semsyekeler/Embedded-AI-Vision-Glass/1_Hardware_Design/gozluk-sema-fiziksel.jpg

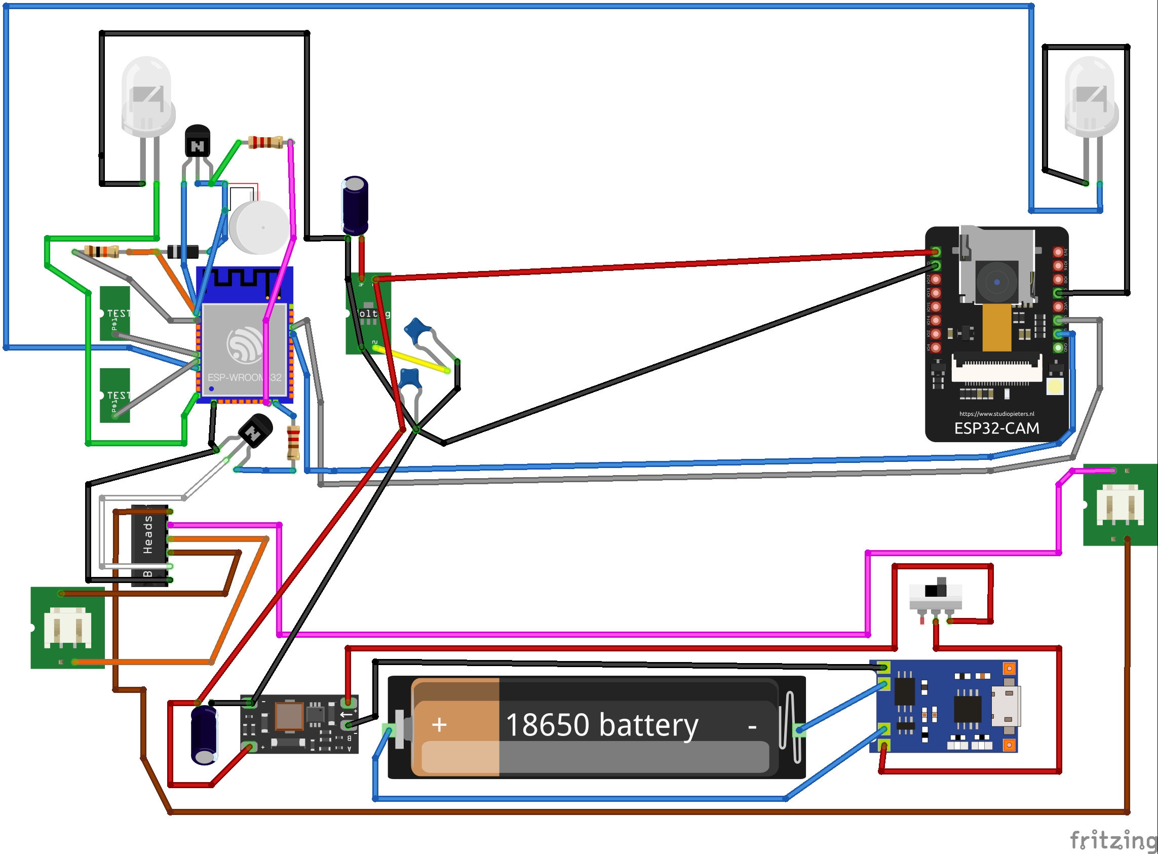
1_Hardware_Design/gozluk-sema-fiziksel.jpg
