semsyekeler/Embedded-AI-Vision-Glass/1_Hardware_Design/gozluk-sema.jpg

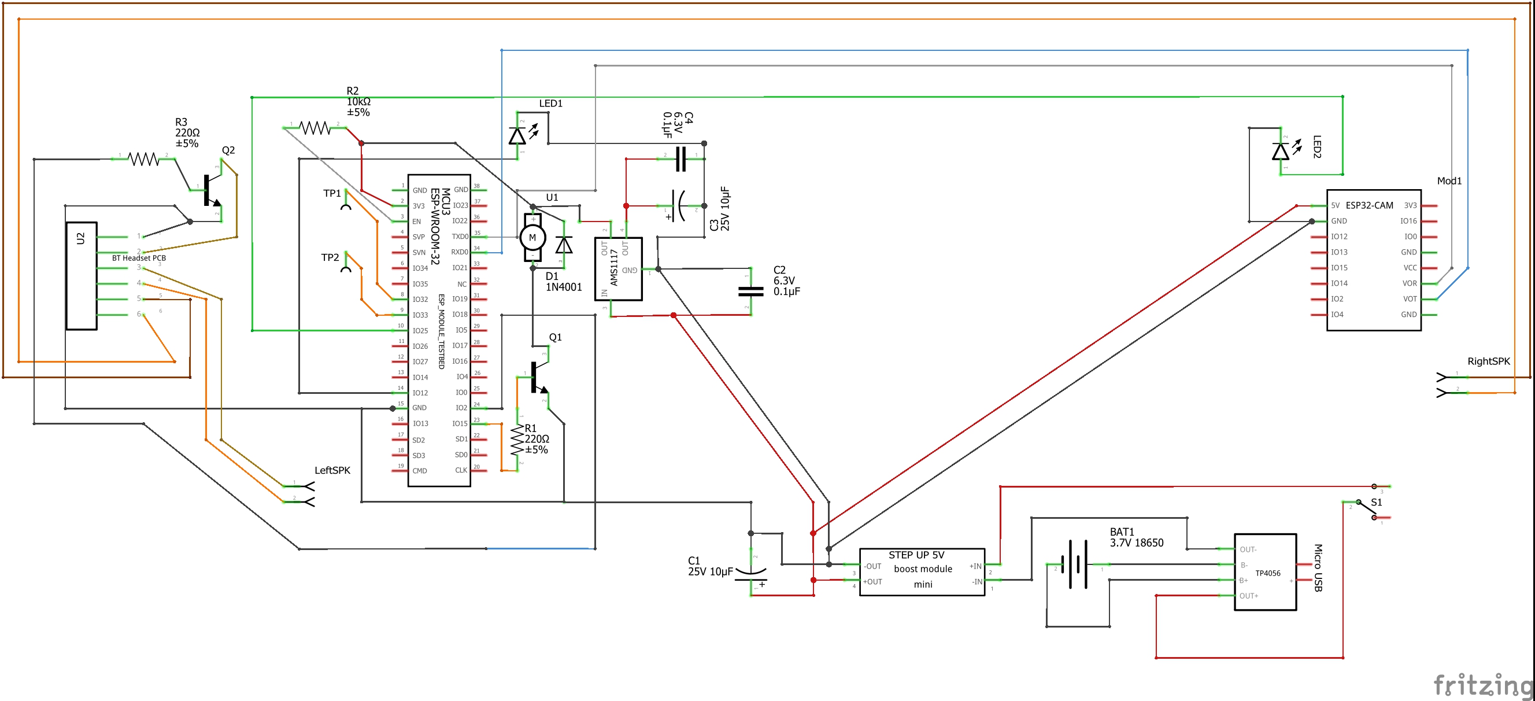
1_Hardware_Design/gozluk-sema.jpg
