semsyekeler/Embedded-AI-Vision-Glass/5_Project_Documentation/Media/2_Competition_and_Awards/award-pose-shoot-upside.jpg

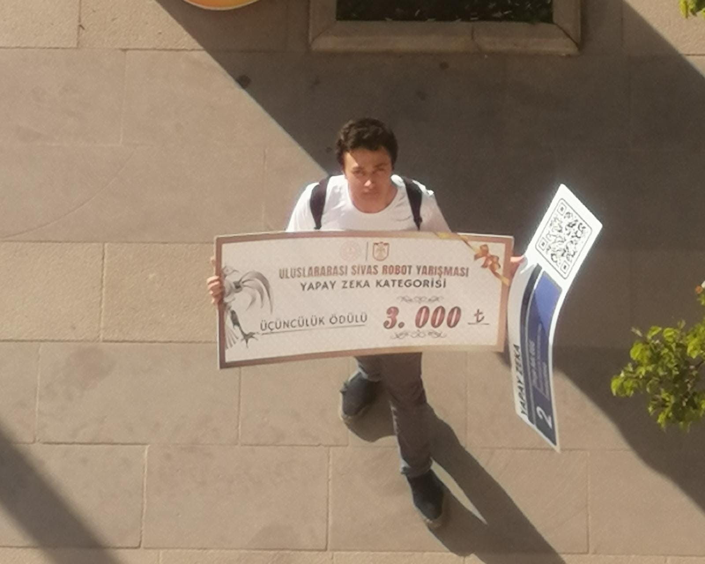
5_Project_Documentation/Media/2_Competition_and_Awards/award-pose-shoot-upside.jpg
