semsyekeler/Embedded-AI-Vision-Glass/5_Project_Documentation/Media/2_Competition_and_Awards/ben-gözüm-kapali-stantta-odul.jpg

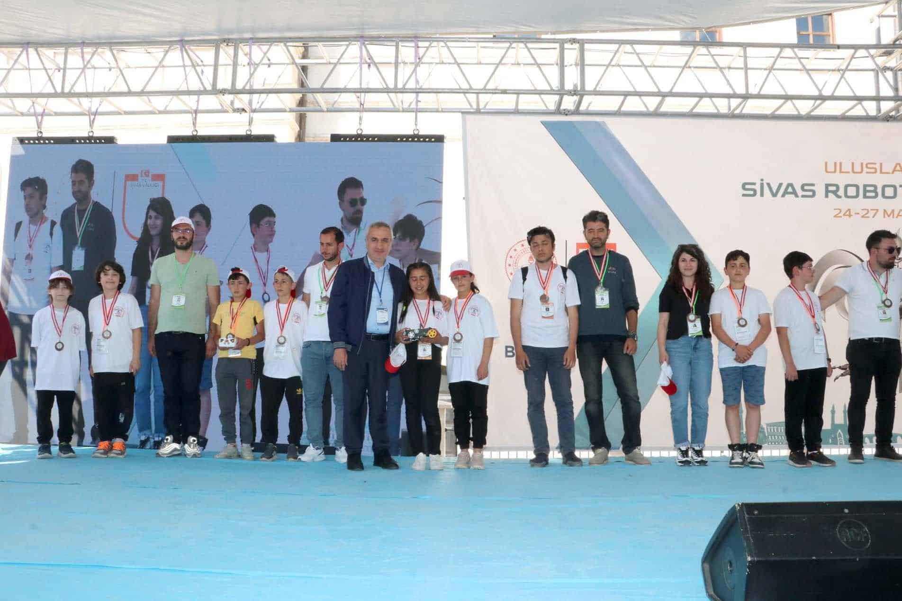
5_Project_Documentation/Media/2_Competition_and_Awards/ben-gözüm-kapali-stantta-odul.jpg
