semsyekeler/Embedded-AI-Vision-Glass/5_Project_Documentation/Media/2_Competition_and_Awards/robotik-team.jpg

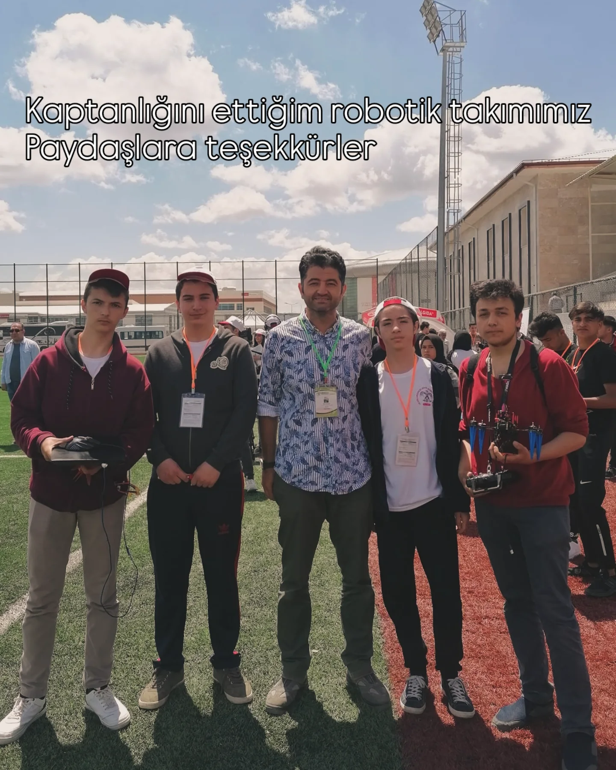
5_Project_Documentation/Media/2_Competition_and_Awards/robotik-team.jpg
