semsyekeler/Embedded-AI-Vision-Glass/5_Project_Documentation/Media/2_Competition_and_Awards/sivas-robotic-comp-happend.jpg

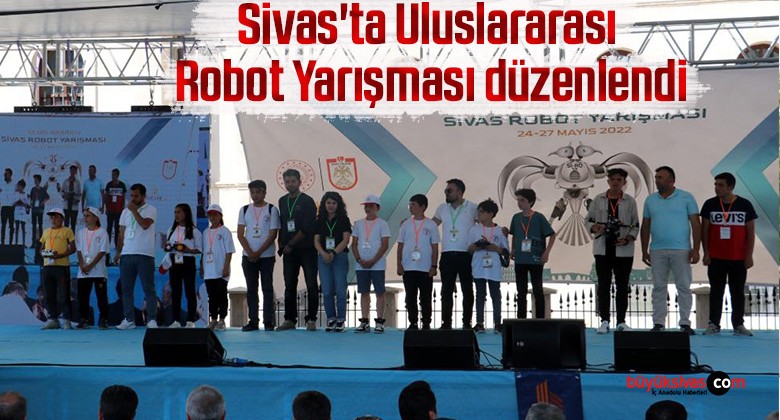
5_Project_Documentation/Media/2_Competition_and_Awards/sivas-robotic-comp-happend.jpg
