semsyekeler/Embedded-AI-Vision-Glass/5_Project_Documentation/Media/3_Demos_and_Presentations/egg-tanitim.jpg

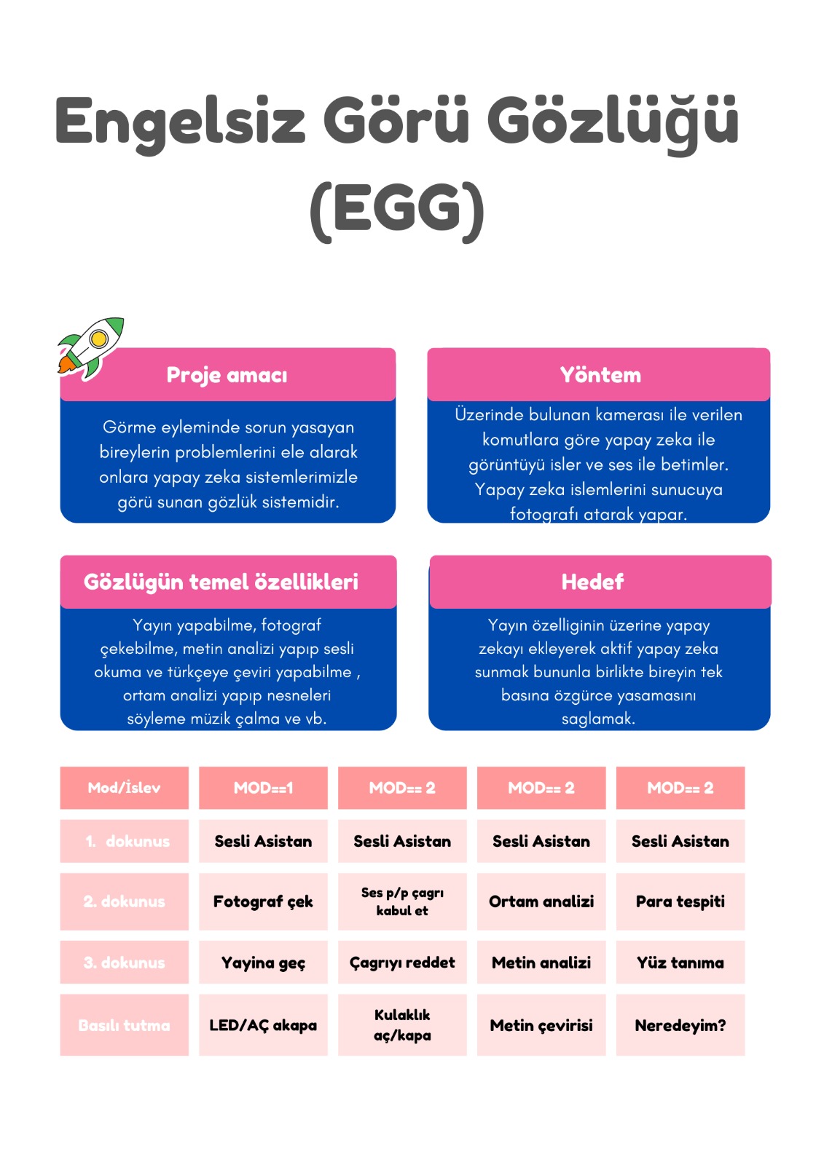
5_Project_Documentation/Media/3_Demos_and_Presentations/egg-tanitim.jpg
