semsyekeler/Embedded-AI-Vision-Glass/5_Project_Documentation/Media/3_Demos_and_Presentations/gozluk-elde-tutulurken.png

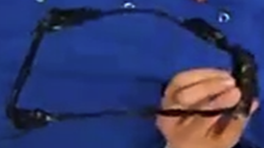
5_Project_Documentation/Media/3_Demos_and_Presentations/gozluk-elde-tutulurken.png
