semsyekeler/Embedded-AI-Vision-Glass/5_Project_Documentation/Reports_and_Presentations/EGG teknofest proje başvurusu .png

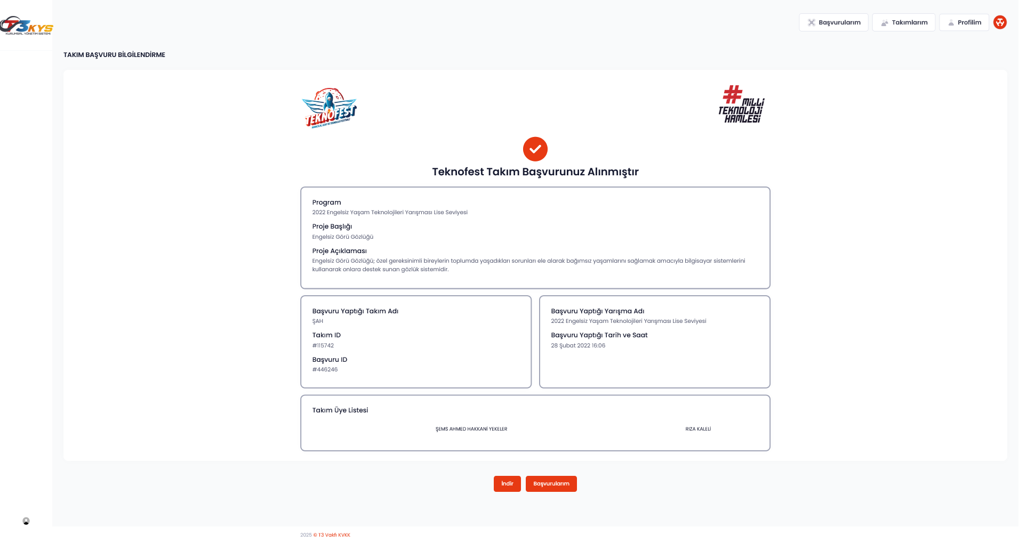
5_Project_Documentation/Reports_and_Presentations/EGG teknofest proje başvurusu .png
