semsyekeler/Embedded-AI-Vision-Glass/5_Project_Documentation/Reports_and_Presentations/ilk prototip.jpg

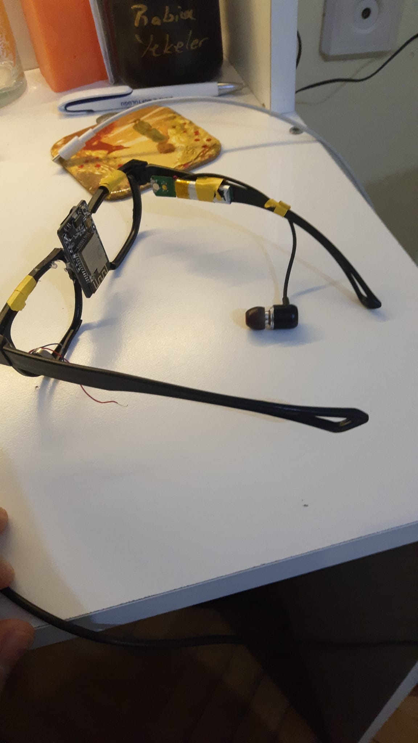
5_Project_Documentation/Reports_and_Presentations/ilk prototip.jpg
