semsyekeler/Embedded-AI-Vision-Glass/5_Project_Documentation/Media/1_Prototyping_and_Assembly/am1117-montaj.png

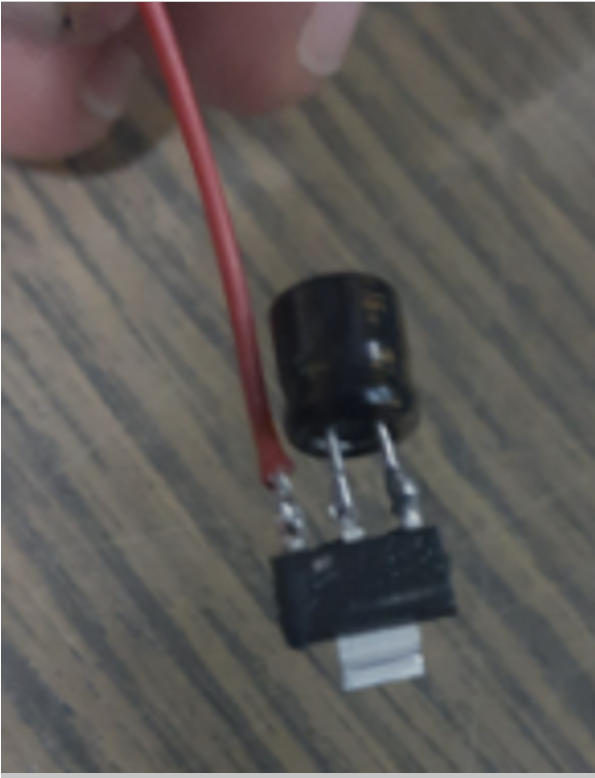
5_Project_Documentation/Media/1_Prototyping_and_Assembly/am1117-montaj.png
