semsyekeler/Embedded-AI-Vision-Glass/5_Project_Documentation/Media/1_Prototyping_and_Assembly/batarya-kismi-montajlanmis.png

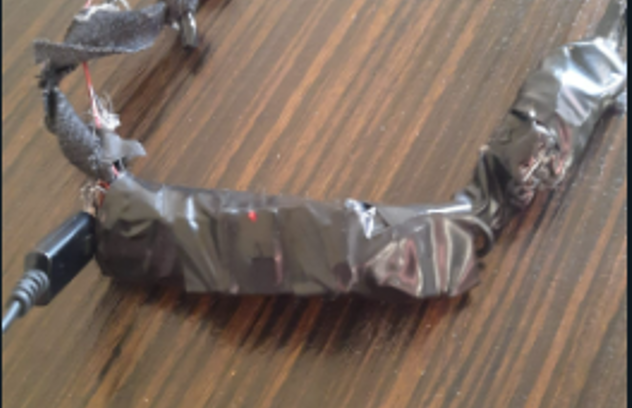
5_Project_Documentation/Media/1_Prototyping_and_Assembly/batarya-kismi-montajlanmis.png
