semsyekeler/Embedded-AI-Vision-Glass/5_Project_Documentation/Media/1_Prototyping_and_Assembly/esp32cam-kismindan-yandan-bakis-montajli-hali-cplk-foto.png

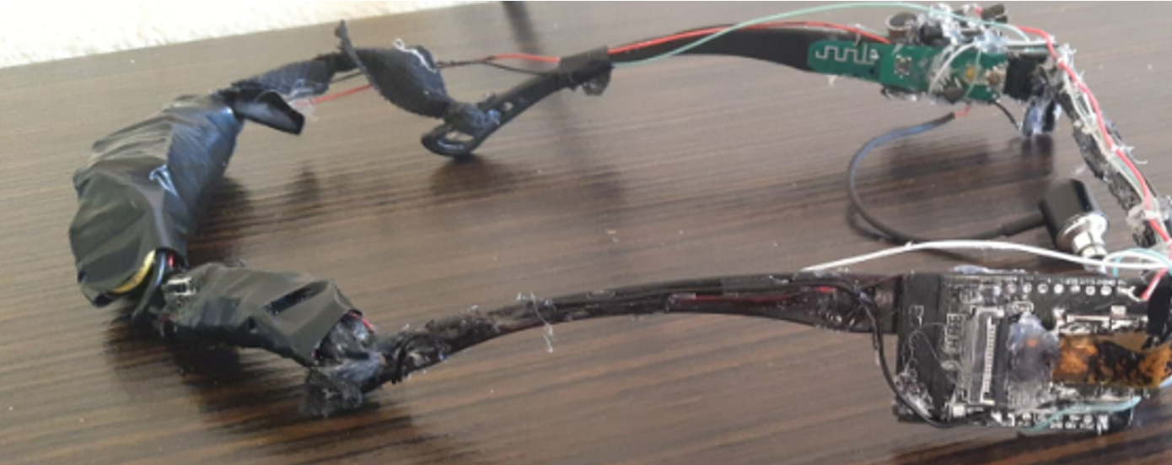
5_Project_Documentation/Media/1_Prototyping_and_Assembly/esp32cam-kismindan-yandan-bakis-montajli-hali-cplk-foto.png
