semsyekeler/Embedded-AI-Vision-Glass/4_Mobile_Application/Source_Code_Android/app/src/main/java/com/my/newproject6/MainActivity.java

package com.my.newproject6;

import android.app.Activity;
import android.app.*;
import android.os.*;
import android.view.*;
import android.view.View.*;
import android.widget.*;
import android.content.*;
import android.content.res.*;
import android.graphics.*;
import android.graphics.drawable.*;
import android.media.*;
import android.net.*;
import android.text.*;
import android.text.style.*;
import android.util.*;
import android.webkit.*;
import android.animation.*;
import android.view.animation.*;
import java.util.*;
import java.util.regex.*;
import java.text.*;
import org.json.*;
import java.util.ArrayList;
import java.util.HashMap;
import android.widget.LinearLayout;
import android.widget.Spinner;
import android.widget.ArrayAdapter;
import android.widget.TextView;
import android.content.SharedPreferences;
import android.os.Bundle;
import java.io.InputStream;
import android.content.Intent;
import android.net.Uri;
import android.view.View;
import com.mannan.translateapi.*;
import android.app.Fragment;
import android.app.FragmentManager;
import android.app.DialogFragment;


public class MainActivity extends  Activity { 
	
	
	private ArrayList<HashMap<String, Object>> btListMap = new ArrayList<>();
	
	private LinearLayout linear1;
	private Spinner spinner1;
	private TextView textview1;
	
	private BluetoothConnect bluetooth;
	private BluetoothConnect.BluetoothConnectionListener _bluetooth_bluetooth_connection_listener;
	private SharedPreferences sharedPrefences;
	private Intent intent = new Intent();
	@Override
	protected void onCreate(Bundle _savedInstanceState) {
		super.onCreate(_savedInstanceState);
		setContentView(R.layout.main);
		initialize(_savedInstanceState);
		initializeLogic();
	}
	
	private void initialize(Bundle _savedInstanceState) {
		
		linear1 = (LinearLayout) findViewById(R.id.linear1);
		spinner1 = (Spinner) findViewById(R.id.spinner1);
		textview1 = (TextView) findViewById(R.id.textview1);
		bluetooth = new BluetoothConnect(this);
		sharedPrefences = getSharedPreferences("bluetoothIcin", Activity.MODE_PRIVATE);
		
		textview1.setOnClickListener(new View.OnClickListener() {
			@Override
			public void onClick(View _view) {
				if (btListMap.get((int)spinner1.getSelectedItemPosition()).get("name").toString().equals("AkıllıGözlük")) {
					sharedPrefences.edit().putString("btName", btListMap.get((int)spinner1.getSelectedItemPosition()).get("name").toString()).commit();
					sharedPrefences.edit().putString("btAddress", btListMap.get((int)spinner1.getSelectedItemPosition()).get("address").toString()).commit();
					intent.setAction(Intent.ACTION_VIEW);
					intent.setClass(getApplicationContext(), PageActivity.class);
					startActivity(intent);
				}
				else {
					SketchwareUtil.showMessage(getApplicationContext(), "Akilli Gozluğu seçtiğinizden emin olun");
				}
			}
		});
		
		_bluetooth_bluetooth_connection_listener = new BluetoothConnect.BluetoothConnectionListener() {
			@Override
			public void onConnected(String _param1, HashMap<String, Object> _param2) {
				final String _tag = _param1;
				final HashMap<String, Object> _deviceData = _param2;
				
			}
			
			@Override
			public void onDataReceived(String _param1, byte[] _param2, int _param3) {
				final String _tag = _param1;
				final String _data = new String(_param2, 0, _param3);
				
			}
			
			@Override
			public void onDataSent(String _param1, byte[] _param2) {
				final String _tag = _param1;
				final String _data = new String(_param2);
				
			}
			
			@Override
			public void onConnectionError(String _param1, String _param2, String _param3) {
				final String _tag = _param1;
				final String _connectionState = _param2;
				final String _errorMessage = _param3;
				
			}
			
			@Override
			public void onConnectionStopped(String _param1) {
				final String _tag = _param1;
				
			}
		};
	}
	
	private void initializeLogic() {
		textview1.setBackground(new GradientDrawable() { public GradientDrawable getIns(int a, int b) { this.setCornerRadius(a); this.setColor(b); return this; } }.getIns((int)999, 0xFF1976D2));
		textview1.setElevation((float)3);
		bluetooth.activateBluetooth();
		bluetooth.getPairedDevices(btListMap);
		spinner1.setAdapter(new Spinner1Adapter(btListMap));
		spinner1.setElevation((float)3);
		if (!sharedPrefences.getString("btName", "").equals("")) {
			intent.setAction(Intent.ACTION_VIEW);
			intent.setClass(getApplicationContext(), PageActivity.class);
			startActivity(intent);
		}
	}
	
	@Override
	protected void onActivityResult(int _requestCode, int _resultCode, Intent _data) {
		
		super.onActivityResult(_requestCode, _resultCode, _data);
		
		switch (_requestCode) {
			
			default:
			break;
		}
	}
	
	public class Spinner1Adapter extends BaseAdapter {
		ArrayList<HashMap<String, Object>> _data;
		public Spinner1Adapter(ArrayList<HashMap<String, Object>> _arr) {
			_data = _arr;
		}
		
		@Override
		public int getCount() {
			return _data.size();
		}
		
		@Override
		public HashMap<String, Object> getItem(int _index) {
			return _data.get(_index);
		}
		
		@Override
		public long getItemId(int _index) {
			return _index;
		}
		@Override
		public View getView(final int _position, View _v, ViewGroup _container) {
			LayoutInflater _inflater = (LayoutInflater)getBaseContext().getSystemService(Context.LAYOUT_INFLATER_SERVICE);
			View _view = _v;
			if (_view == null) {
				_view = _inflater.inflate(R.layout.bt_item, null);
			}
			
			final LinearLayout linear1 = (LinearLayout) _view.findViewById(R.id.linear1);
			final TextView bt_name = (TextView) _view.findViewById(R.id.bt_name);
			
			bt_name.setText(_data.get((int)_position).get("name").toString());
			
			return _view;
		}
	}
	
	@Deprecated
	public void showMessage(String _s) {
		Toast.makeText(getApplicationContext(), _s, Toast.LENGTH_SHORT).show();
	}
	
	@Deprecated
	public int getLocationX(View _v) {
		int _location[] = new int[2];
		_v.getLocationInWindow(_location);
		return _location[0];
	}
	
	@Deprecated
	public int getLocationY(View _v) {
		int _location[] = new int[2];
		_v.getLocationInWindow(_location);
		return _location[1];
	}
	
	@Deprecated
	public int getRandom(int _min, int _max) {
		Random random = new Random();
		return random.nextInt(_max - _min + 1) + _min;
	}
	
	@Deprecated
	public ArrayList<Double> getCheckedItemPositionsToArray(ListView _list) {
		ArrayList<Double> _result = new ArrayList<Double>();
		SparseBooleanArray _arr = _list.getCheckedItemPositions();
		for (int _iIdx = 0; _iIdx < _arr.size(); _iIdx++) {
			if (_arr.valueAt(_iIdx))
			_result.add((double)_arr.keyAt(_iIdx));
		}
		return _result;
	}
	
	@Deprecated
	public float getDip(int _input){
		return TypedValue.applyDimension(TypedValue.COMPLEX_UNIT_DIP, _input, getResources().getDisplayMetrics());
	}
	
	@Deprecated
	public int getDisplayWidthPixels(){
		return getResources().getDisplayMetrics().widthPixels;
	}
	
	@Deprecated
	public int getDisplayHeightPixels(){
		return getResources().getDisplayMetrics().heightPixels;
	}
	
}
